jdimpson/PowerHolder/assets/IMG_20200927_230835.jpg

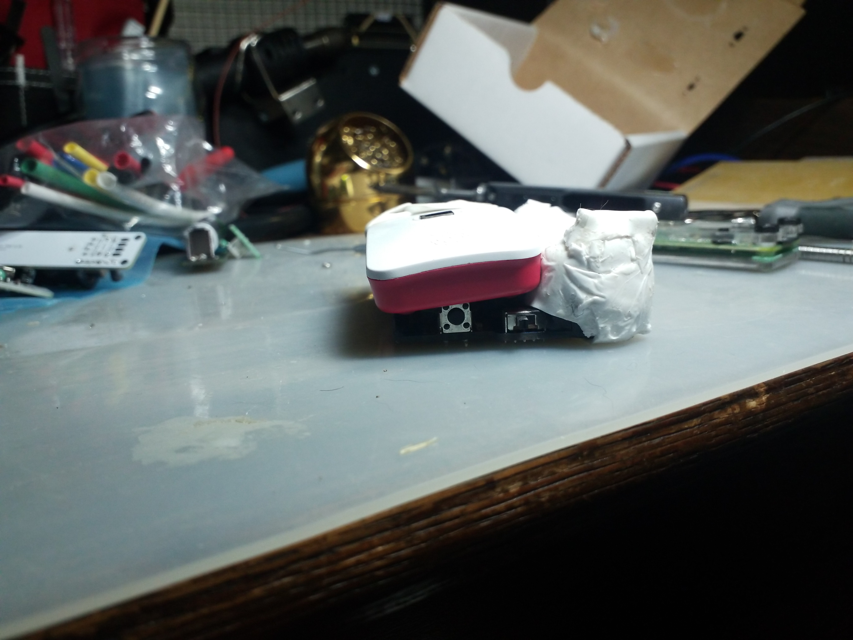
assets/IMG_20200927_230835.jpg
