jdimpson/PowerHolder/assets/IMG_20200927_230856.jpg

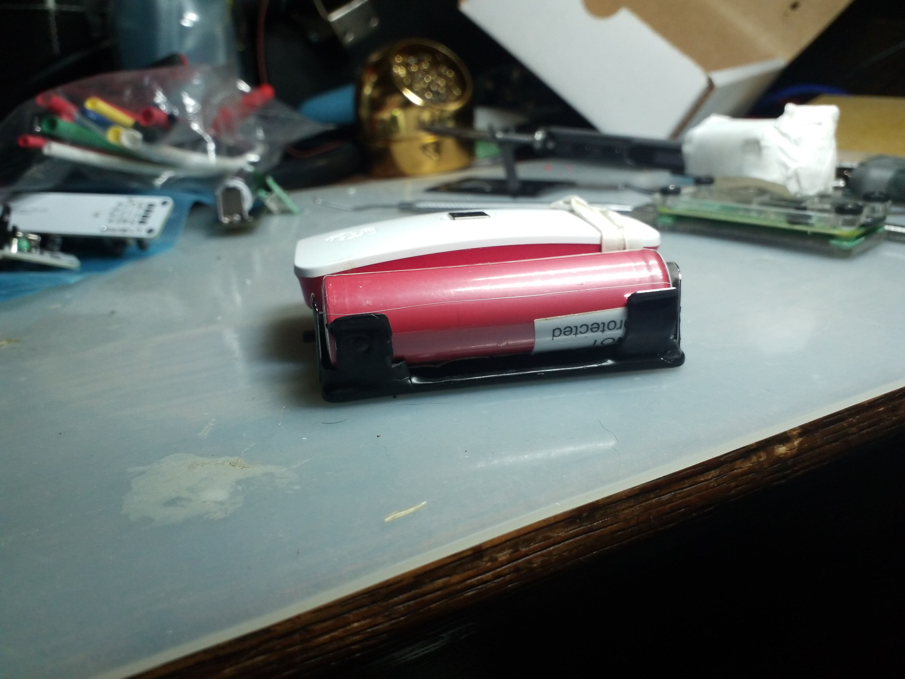
assets/IMG_20200927_230856.jpg
