jdimpson/PowerHolder/assets/IMG_20200927_230904.jpg

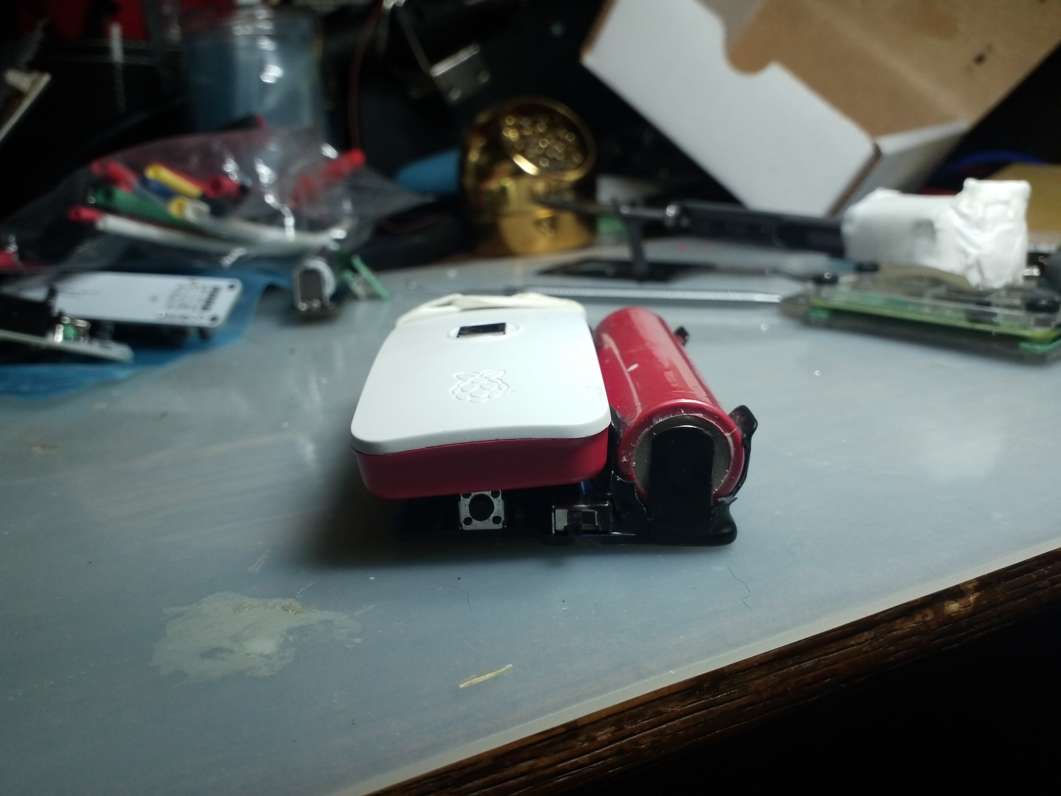
assets/IMG_20200927_230904.jpg
