jdimpson/PowerHolder/assets/IMG_20200927_230913.jpg

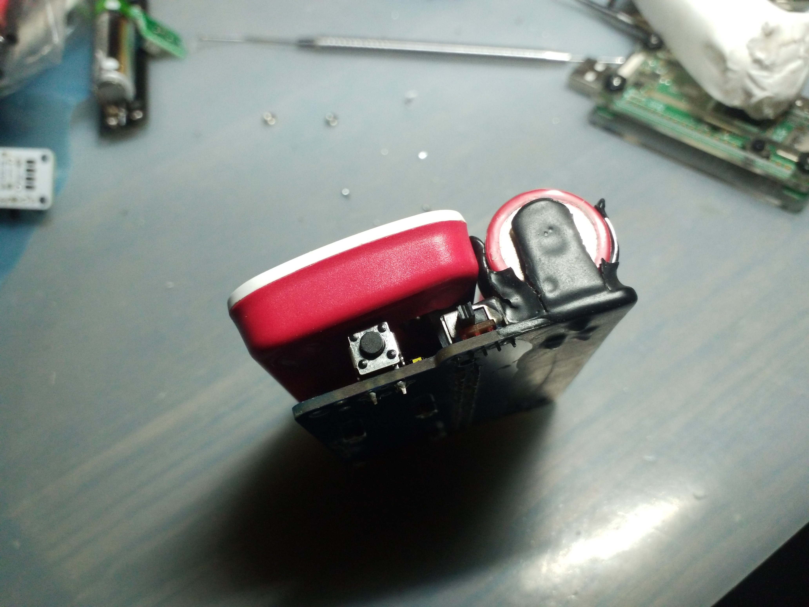
assets/IMG_20200927_230913.jpg
