jdimpson/PowerHolder/assets/IMG_20200927_230941.jpg

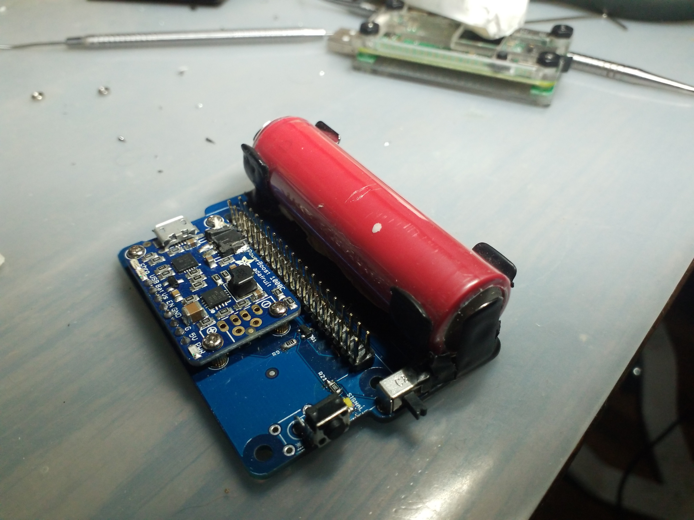
assets/IMG_20200927_230941.jpg
