jdimpson/PowerHolder/assets/IMG_20200927_230950.jpg

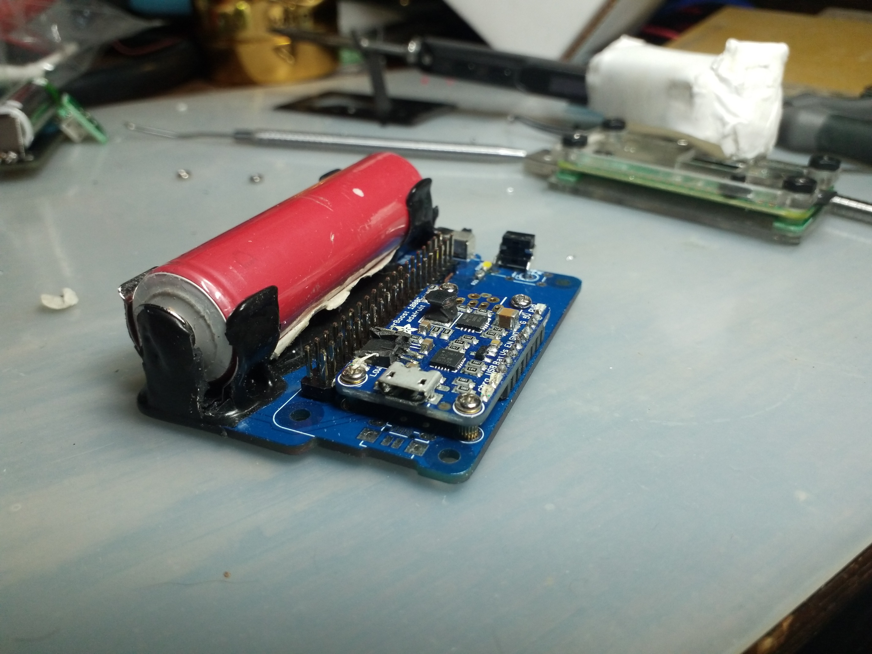
assets/IMG_20200927_230950.jpg
