jdimpson/PowerHolder/assets/IMG_20200927_231023.jpg

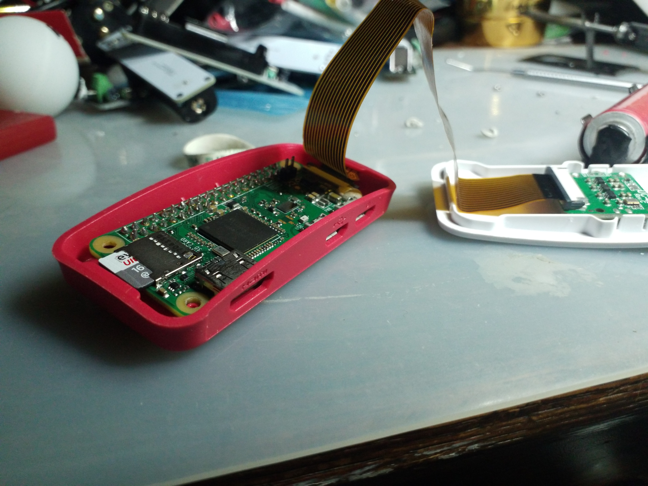
assets/IMG_20200927_231023.jpg
