jdimpson/PowerHolder/assets/IMG_20200927_231035.jpg

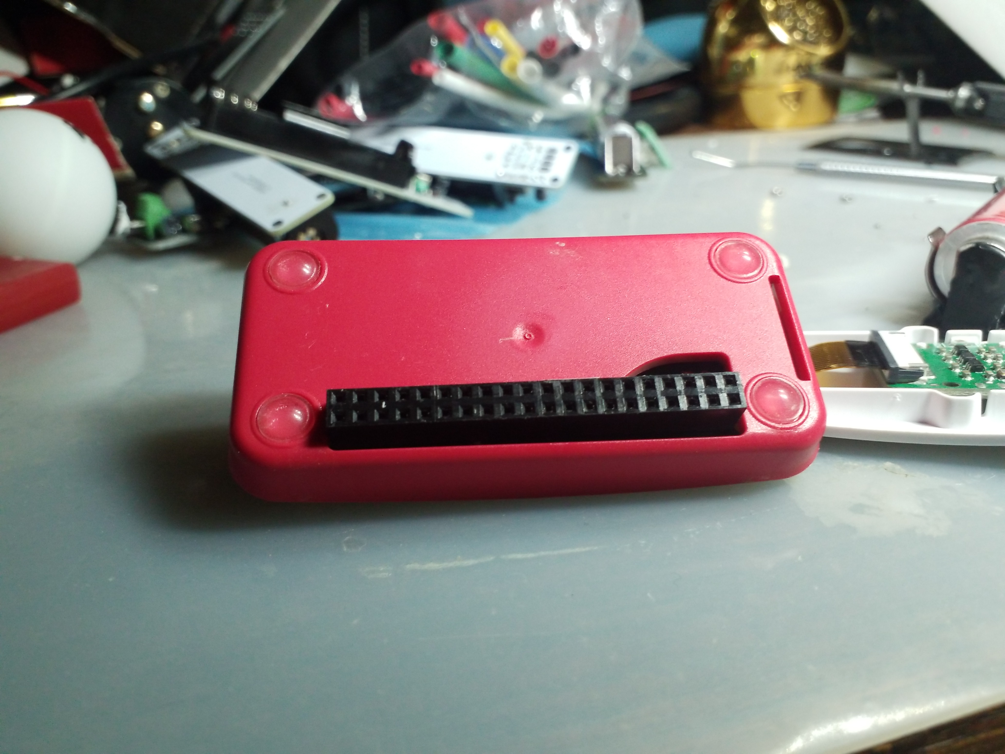
assets/IMG_20200927_231035.jpg
