jdimpson/PowerHolder/assets/IMG_20200927_231217.jpg

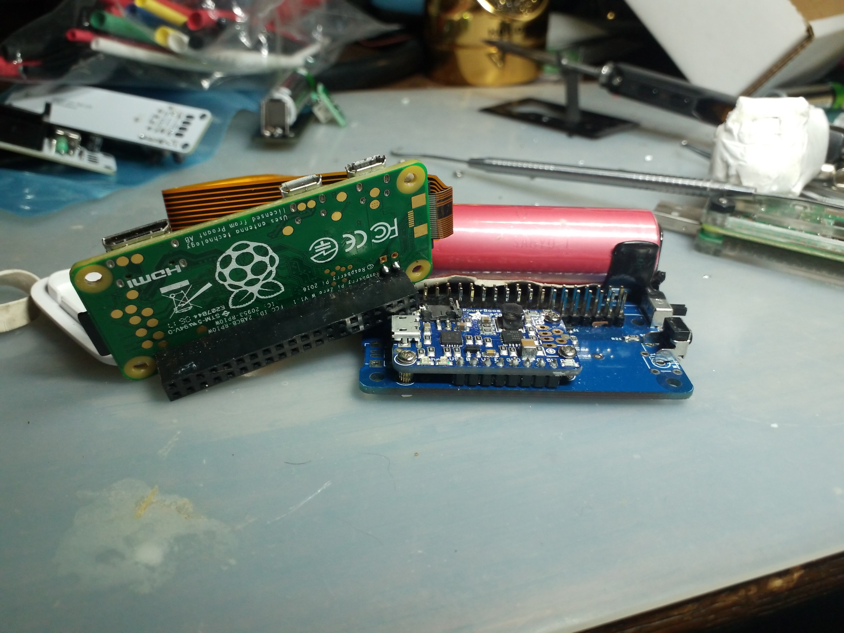
assets/IMG_20200927_231217.jpg
